Grittie/Beertracker-HUB/docs/assets/fritzing/0.1/RFID RC522_schem.png

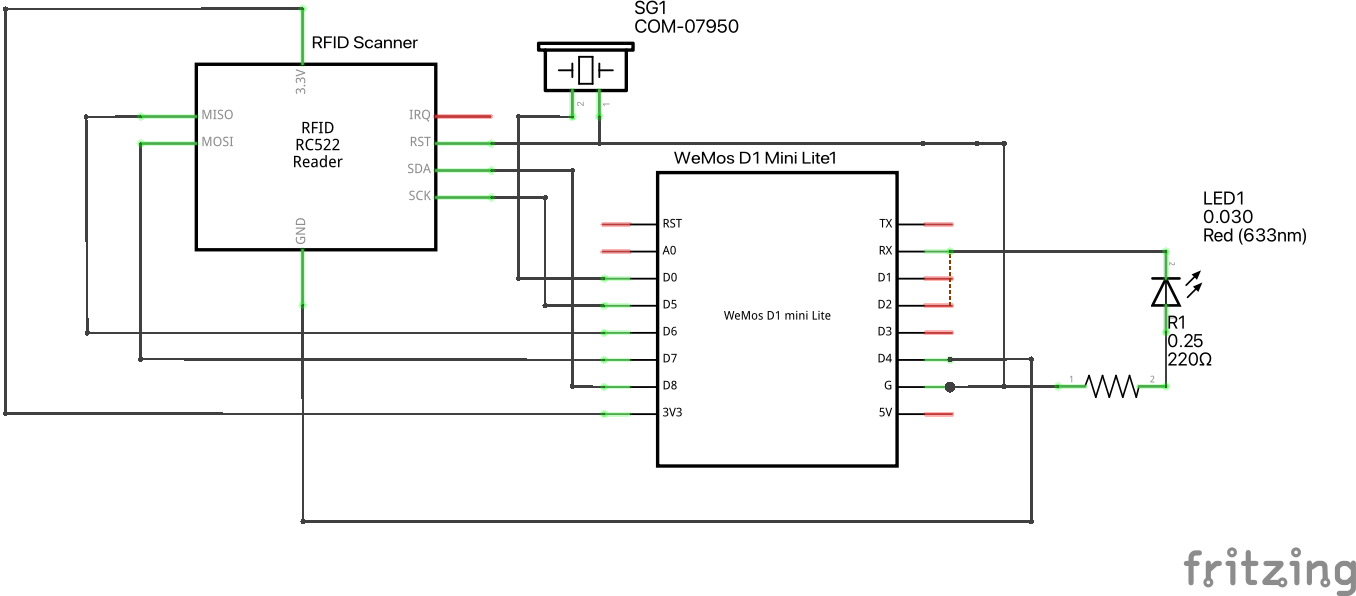
docs/assets/fritzing/0.1/RFID RC522_schem.png
