Grittie/Beertracker-HUB/docs/assets/fritzing/0.3/RFID RC522_schem.png

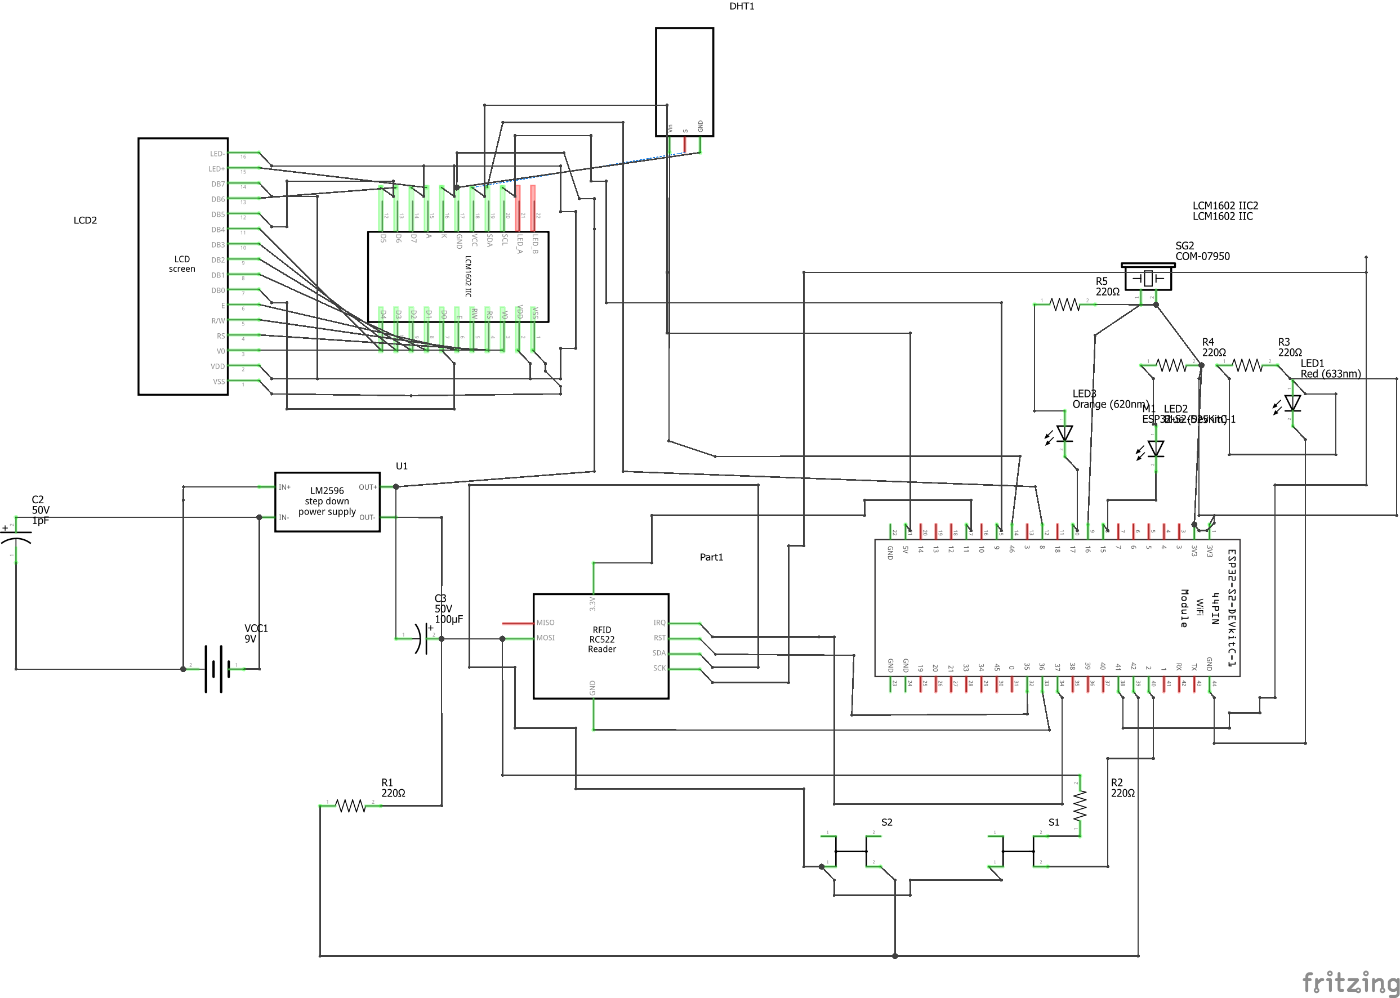
docs/assets/fritzing/0.3/RFID RC522_schem.png
