Grittie/Beertracker-HUB/docs/assets/images/conclude/6.png

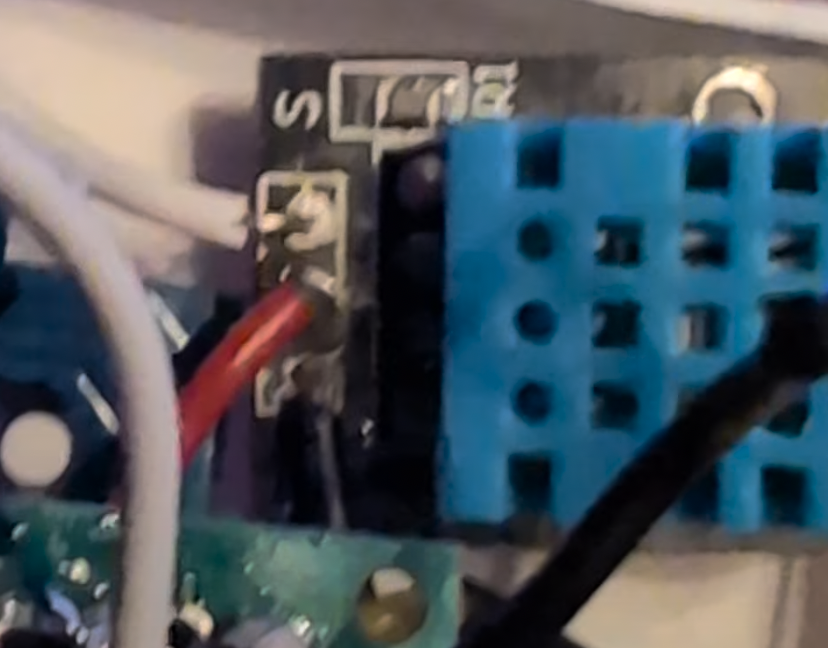
docs/assets/images/conclude/6.png
